ardaanbhatia7/Active-Notch-Filter-Cigar-Box-Electric-Guitar/ActiveNotchFilter.asc

C1: cap; 162.4n
C2: cap; 81.2n
C3: cap; 81.2n
R1: res; 10k
R2: res; 10k
R3: res; 5k
R4: res; 6.8k
R5: res; 220k
R6: res; 10k
R7: res; 1k
U1: UniversalOpAmp1; En=0 Enk=0 In=0 Ink=0 Rin=100Meg
U2: UniversalOpAmp1; En=0 Enk=0 In=0 Ink=0 Rin=100Meg
U3: UniversalOpAmp1
V1: voltage; SINE(0 1 196); AC 1
V2: voltage; -9
V3: voltage; 9
Named nets: 0
.ac lin 10k 150 250
