ardaanbhatia7/Active-Notch-Filter-Cigar-Box-Electric-Guitar/PassiveNotchFilter.asc

C1: cap; 81.2n
C2: cap; 81.2n
C3: cap; 162.4n
R1: Res; 10k
R2: Res; 10k
R3: Res; 5k
V1: Voltage; SINE(); AC 1
Named nets: 0, Vin, Vout
.ac lin 1000 1 500
