ardaanbhatia7/Active-Notch-Filter-Cigar-Box-Electric-Guitar/1719.kicad_sch

## KiCad design 1719.kicad_sch (2026-05-25)

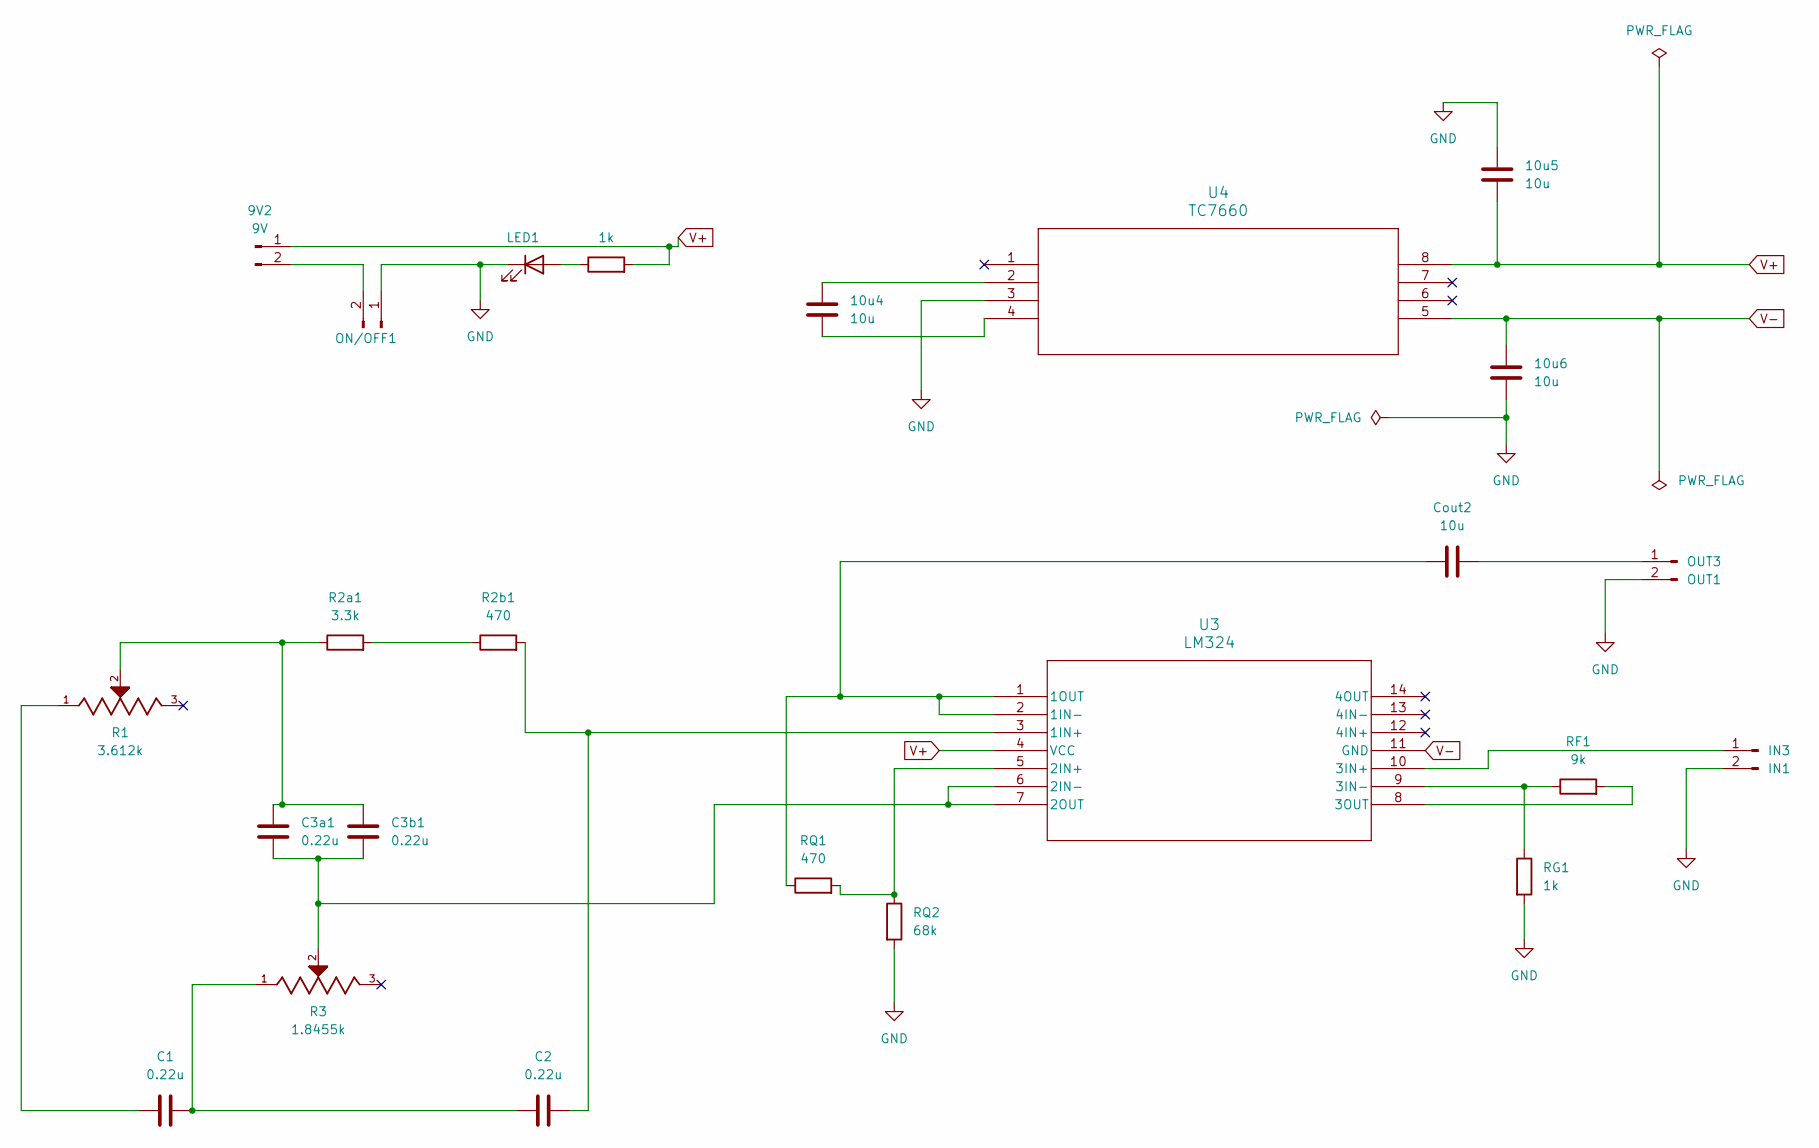
[picture p12: schematic 1719.kicad_sch]

Parts:
9V2: 9V; PinHeader_1x02_P2.54mm_Vertical
10u4, 10u5, 10u6: 10u; C_0805_2012Metric_Pad1.18x1.45mm_HandSolder
C1, C2, C3a1, C3b1: 0.22u; C_0805_2012Metric_Pad1.18x1.45mm_HandSolder
Cout2: 10u; C_0805_2012Metric_Pad1.18x1.45mm_HandSolder
IN1: IN3; PinHeader_1x02_P2.54mm_Vertical
LED1: LED; PinHeader_1x02_P2.54mm_Vertical
ON/OFF1: Conn_01x02_Pin; PinHeader_1x02_P2.54mm_Vertical
OUT1: OUT3; PinHeader_1x02_P2.54mm_Vertical
R1: 3.612k; TRIM_3296W-1-502RLF; PARTREV 05/16; DigiKey_Part_Number 118-3296W-1-502RLFCT-ND
R2a1: 3.3k; R_0805_2012Metric_Pad1.20x1.40mm_HandSolder
R2b1: 470; R_0805_2012Metric_Pad1.20x1.40mm_HandSolder
R3: 1.8455k; TRIM_3296W-1-502RLF; PARTREV 05/16; DigiKey_Part_Number 118-3296W-1-502RLFCT-ND
R11: 1k; R_0805_2012Metric_Pad1.20x1.40mm_HandSolder
RF1: 9k; R_0805_2012Metric_Pad1.20x1.40mm_HandSolder
RG1: 1k; R_0805_2012Metric_Pad1.20x1.40mm_HandSolder
RQ1: 470; R_0805_2012Metric_Pad1.20x1.40mm_HandSolder
RQ2: 68k; R_0805_2012Metric_Pad1.20x1.40mm_HandSolder
U3: LM324; Op_amp
U4: TC7660; SOIC8-N_MC_MCH

Connections:
GND: 10u5.1, 10u6.1, IN1.2, LED1.1 (K), ON/OFF1.1, OUT1.2, RG1.2, RQ2.2, U4.3
unnamed: 9V2.2, ON/OFF1.2
unnamed: 10u4.1, U4.2
unnamed: 10u4.2, U4.4
unnamed: C1.1, R1.1
unnamed: C1.2, C2.1, R3.1
unnamed: C2.2, R2b1.2, U3.3 (1IN+)
unnamed: C3a1.1, C3b1.1, R1.2, R2a1.1
unnamed: C3a1.2, C3b1.2, R3.2, U3.6 (2IN-), U3.7 (2OUT)
unnamed: Cout2.1, RQ1.1, U3.1 (1OUT), U3.2 (1IN-)
unnamed: Cout2.2, OUT1.1
unnamed: IN1.1, U3.10 (3IN+)
unnamed: LED1.2 (A), R11.1
unnamed: R2a1.2, R2b1.1
unnamed: RF1.1, RG1.1, U3.9 (3IN-)
unnamed: RF1.2, U3.8 (3OUT)
unnamed: RQ1.2, RQ2.1, U3.5 (2IN+)
V+: 9V2.1, 10u5.2, R11.2, U3.4 (VCC), U4.8
V-: 10u6.2, U3.11 (GND), U4.5
